kmio42/moon-display/src/display_mode.h

#ifndef DISPLAY_MODE_H
#define DISPLAY_MODE_H

// Anzeigemodi (persistent als configDisplayMode)
constexpr int DISPLAY_MODE_MOON  = 0;  // Live-Mond
constexpr int DISPLAY_MODE_CLOCK = 1;  // 24h-Uhr mit Sonnen- und Mondzeigern

#endif // DISPLAY_MODE_H
